kagjerde/Arduino-based-soldering-station/Arduino/Weller.c

#include <avr/pgmspace.h>
 // 'last ned', 128x42px
const unsigned char Weller [] PROGMEM = {
  0x00, 0x00, 0x00, 0x00, 0x00, 0x00, 0x00, 0x00, 0x80, 0x08, 0x00, 0x00, 0x00, 0x00, 0x00, 0x00, 
  0xff, 0xf8, 0x00, 0xe0, 0x3f, 0xf0, 0x00, 0x07, 0x80, 0x78, 0x00, 0x00, 0x00, 0x00, 0x00, 0x00, 
  0xff, 0xf8, 0x0f, 0xe0, 0x3f, 0xf0, 0x00, 0x3f, 0x83, 0xf8, 0x00, 0x00, 0x00, 0x00, 0x00, 0x00, 
  0x3f, 0xe0, 0x3f, 0xe0, 0x1f, 0xf0, 0x00, 0xff, 0x8f, 0xf8, 0x00, 0x00, 0x00, 0x00, 0x00, 0x00, 
  0x3f, 0xe0, 0x1f, 0xe0, 0x07, 0xe0, 0x00, 0xff, 0x8f, 0xf8, 0x00, 0x00, 0x00, 0x00, 0x00, 0x00, 
  0x1f, 0xe0, 0x1f, 0xf0, 0x07, 0xc0, 0x00, 0xff, 0x8f, 0xf8, 0x00, 0x00, 0x00, 0x00, 0x00, 0xf0, 
  0x1f, 0xe0, 0x1f, 0xf0, 0x07, 0x80, 0x00, 0x1f, 0x83, 0xf8, 0x00, 0x00, 0x00, 0x00, 0x01, 0x08, 
  0x1f, 0xe0, 0x1f, 0xf0, 0x07, 0x80, 0x00, 0x1f, 0x83, 0xf8, 0x00, 0x00, 0x00, 0x00, 0x02, 0x14, 
  0x1f, 0xe0, 0x0f, 0xf0, 0x07, 0x00, 0x00, 0x1f, 0x83, 0xf8, 0x00, 0x00, 0x00, 0x00, 0x02, 0x10, 
  0x1f, 0xf0, 0x0f, 0xf8, 0x07, 0x00, 0x00, 0x1f, 0x83, 0xf8, 0x00, 0x00, 0x00, 0x00, 0x02, 0x20, 
  0x0f, 0xf0, 0x0f, 0xf8, 0x07, 0x00, 0x00, 0x1f, 0x83, 0xf8, 0x00, 0x00, 0x00, 0x00, 0x02, 0x14, 
  0x0f, 0xf0, 0x1f, 0xf8, 0x06, 0x00, 0x00, 0x1f, 0x83, 0xf8, 0x00, 0x00, 0x00, 0x00, 0x01, 0x08, 
  0x0f, 0xf0, 0x1f, 0xf8, 0x0e, 0x03, 0xe0, 0x1f, 0x83, 0xf8, 0x03, 0xf0, 0x00, 0x81, 0xe0, 0xf0, 
  0x0f, 0xf0, 0x1f, 0xfc, 0x0e, 0x1f, 0xf8, 0x1f, 0x83, 0xf8, 0x0f, 0xfc, 0x07, 0xc3, 0xf0, 0x00, 
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
  0x00, 0x00, 0x00, 0x00, 0x00, 0x00, 0x0f, 0xff, 0xf8, 0x00, 0x7e, 0x0f, 0xc0, 0x00, 0x00, 0x00, 
  0x00, 0x00, 0x00, 0x00, 0x00, 0x00, 0x1f, 0xff, 0xb8, 0x00, 0xf8, 0x03, 0xe0, 0x00, 0x00, 0x00, 
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
};
